brNX/gamecube-rf24-remote/rf24/RF24_config.h

/*
 Copyright (C) 2011 J. Coliz <maniacbug@ymail.com>

 This program is free software; you can redistribute it and/or
 modify it under the terms of the GNU General Public License
 version 2 as published by the Free Software Foundation.
 */

#ifndef __RF24_CONFIG_H__
#define __RF24_CONFIG_H__

#include <stddef.h>
#include <stdint.h>
#include <stdio.h>
#include <string.h>
#include <avr/pgmspace.h>
#include <avr/pgmspace.h>
#define PRIPSTR "%S"

#undef SERIAL_DEBUG
#ifdef SERIAL_DEBUG
#define IF_SERIAL_DEBUG(x) ({x;})
#else
#define IF_SERIAL_DEBUG(x)
#endif

// Avoid spurious warnings
#if 1
#undef PROGMEM
#define PROGMEM __attribute__(( section(".progmem.data") ))
#undef PSTR
#define PSTR(s) (__extension__({static const char __c[] PROGMEM = (s); &__c[0];}))
#endif





//typedef char const char;
//typedef uint16_t prog_uint16_t;
//#define PSTR(x) (x)
//#define printf_P printf
//#define strlen_P strlen
//#define PROGMEM
//#define pgm_read_word(p) (*(p))
//#define PRIPSTR "%s"

#ifndef ARDUINO

#define max(a,b) \
   ({ __typeof__ (a) _a = (a); \
       __typeof__ (b) _b = (b); \
     _a > _b ? _a : _b; })

#define min(a,b) \
   ({ __typeof__ (a) _a = (a); \
       __typeof__ (b) _b = (b); \
     _a < _b ? _a : _b; })

#endif


#endif // __RF24_CONFIG_H__
// vim:ai:cin:sts=2 sw=2 ft=cpp
