brNX/gamecube-rf24-remote/rf24/spi.h

/*
 * spi.h
 *
 *  Created on: Apr 21, 2013
 *      Author: bgouveia
 */

#ifndef SPI_H_
#define SPI_H_

#include <stdint.h>

#include <avr/io.h>
#include <avr/interrupt.h>  /* for sei() */
#include <util/delay.h>     /* for _delay_ms() */

void spi_init(unsigned long bitrate,unsigned long datawidth);

uint8_t spi_transferByte(uint8_t _data);

void spi_cs_low();
void spi_cs_high();

void spi_ce_low();
void spi_ce_high();

#endif /* SPI_H_ */
